leobotmanuel/EduBasica/esquemas/img/EduBasicaV2.png

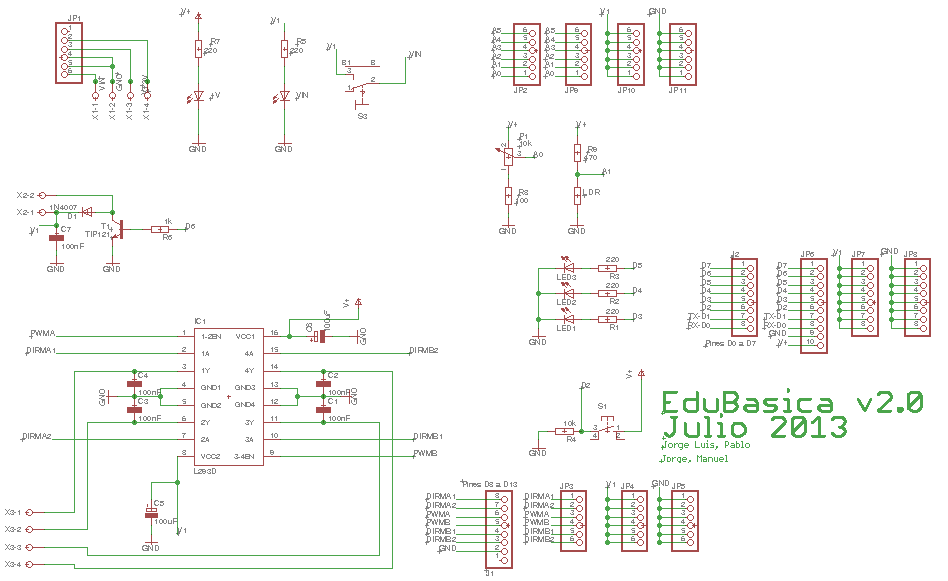
esquemas/img/EduBasicaV2.png
