leobotmanuel/EduBasica/esquemas/img/L293motores.png

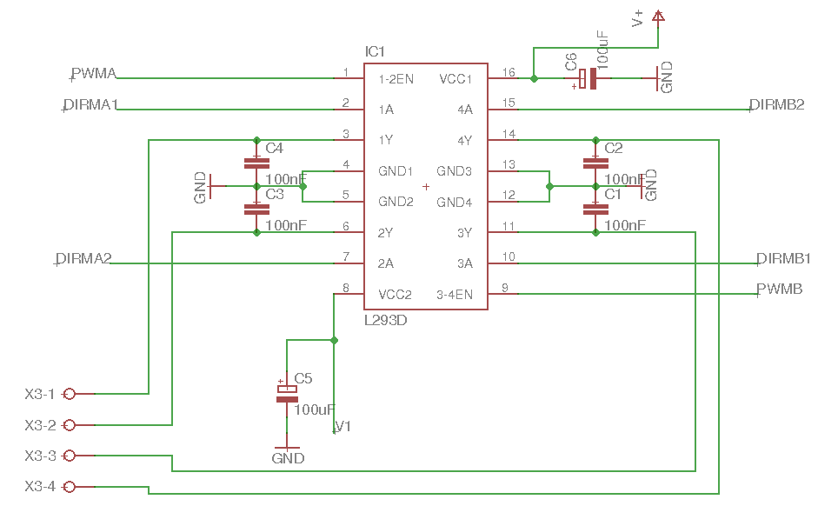
esquemas/img/L293motores.png
