leobotmanuel/EduBasica/esquemas/img/SalidaPotencia.png

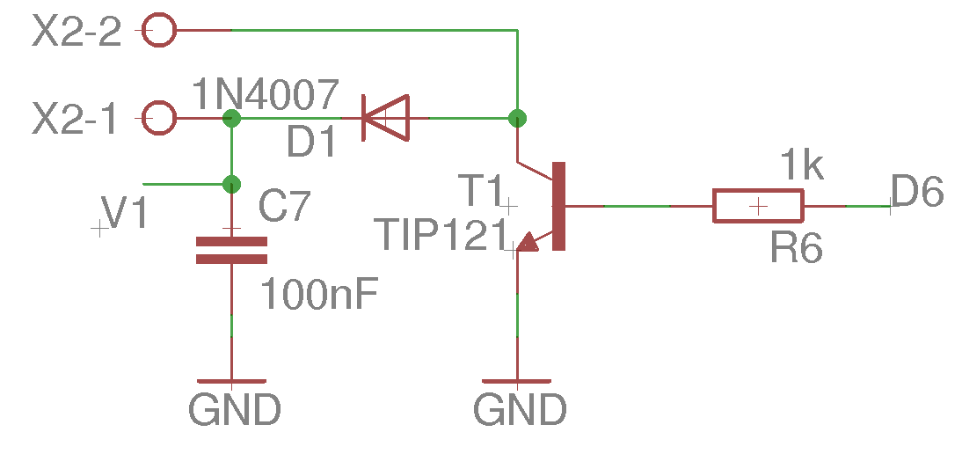
esquemas/img/SalidaPotencia.png
