leobotmanuel/EduBasica/software/04_Sensores/02_Potenciometro/img/potenciometro_cirEdubasica.png

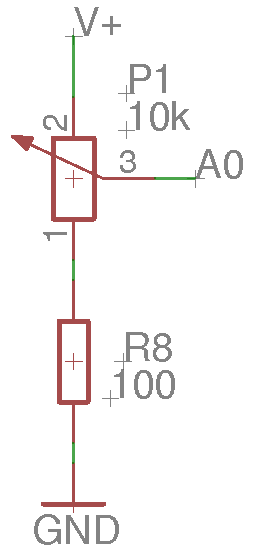
software/04_Sensores/02_Potenciometro/img/potenciometro_cirEdubasica.png
